hari-vickey/The-Eagle-Eye/ros_packages/swarmrobot/models/arena_s2/meshes/Stage2/texture.png

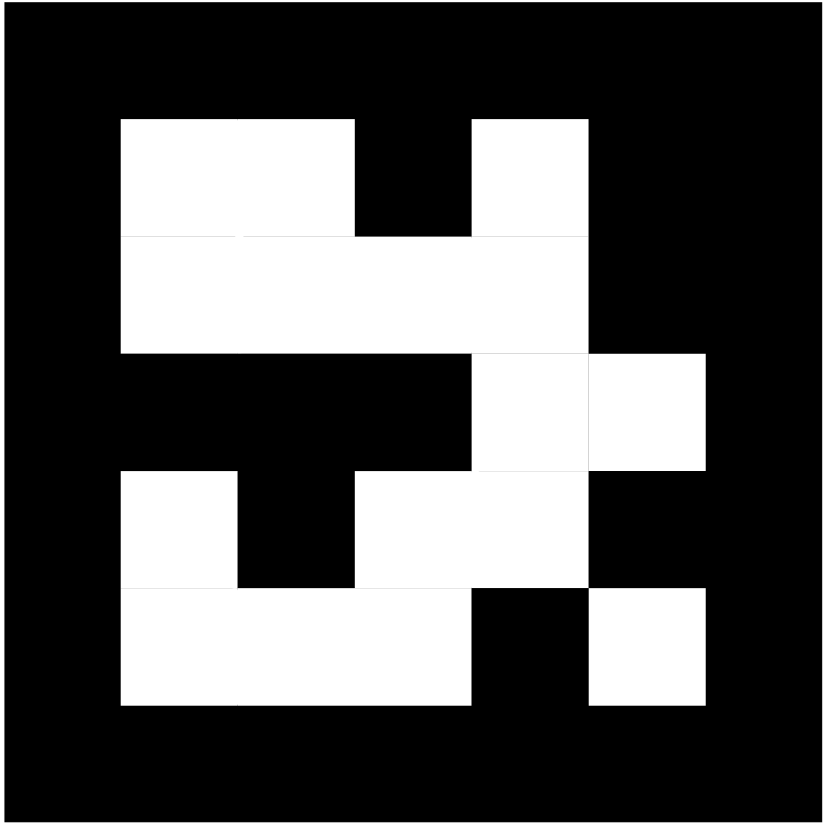
ros_packages/swarmrobot/models/arena_s2/meshes/Stage2/texture.png
