hari-vickey/The-Eagle-Eye/ros_packages/swarmrobot/models/arena_s2/meshes/Stage2/texture_6.png

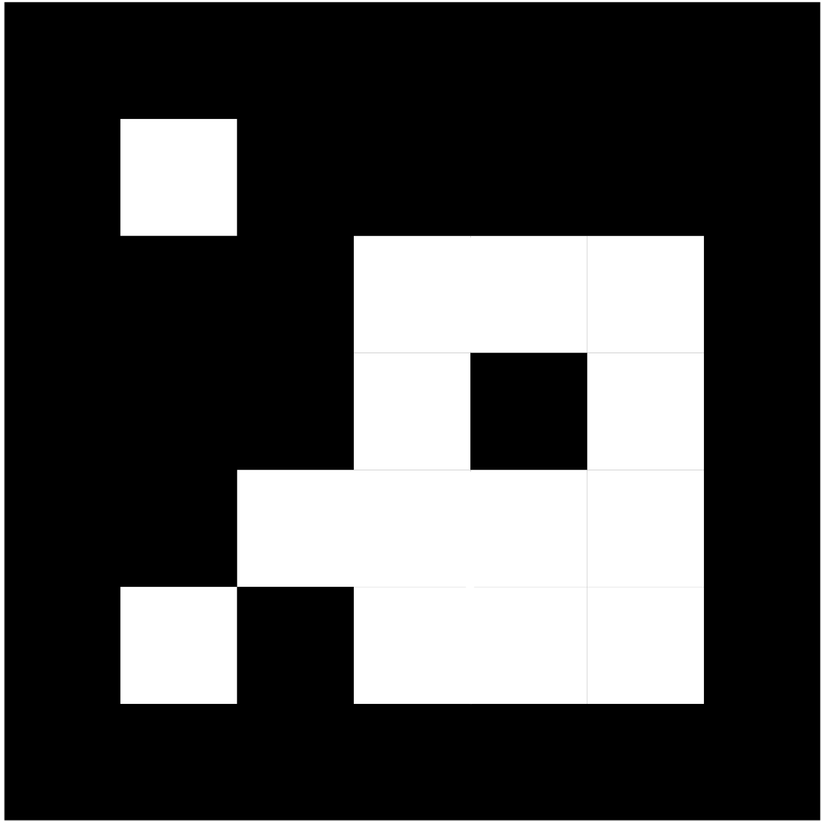
ros_packages/swarmrobot/models/arena_s2/meshes/Stage2/texture_6.png
