hari-vickey/The-Eagle-Eye/ros_packages/grid_bot_description/meshes/identifier_1.stl

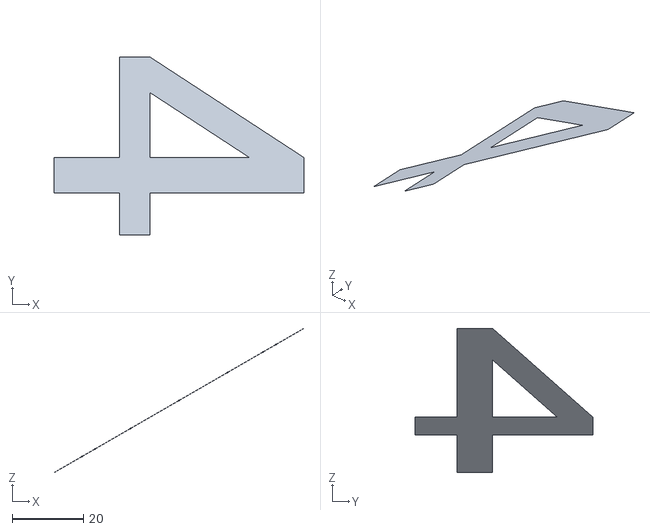
[picture p28: CAD file, 2021-12-07]
ros_packages/grid_bot_description/meshes/identifier_1.stl
70.4 x 50.0 x 40.7
