hari-vickey/The-Eagle-Eye/ros_packages/bot_description/grid_bot_3_description/meshes/identifier_1.stl

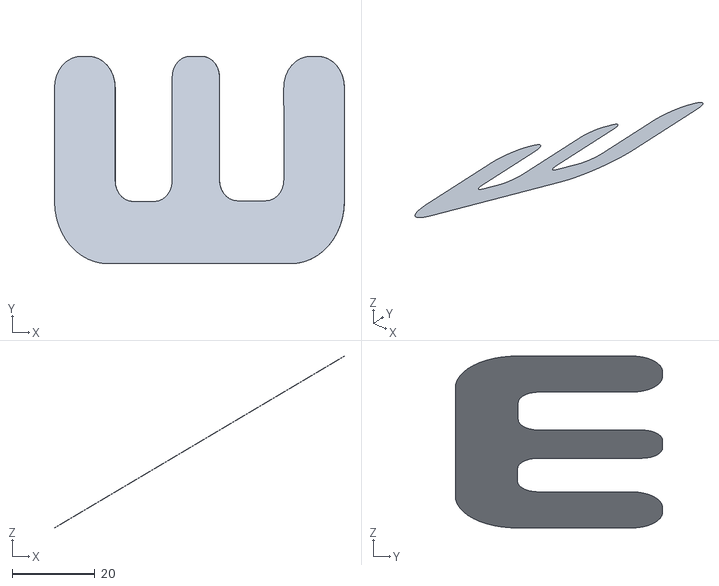
[picture p29: CAD file, 2021-12-07]
ros_packages/bot_description/grid_bot_3_description/meshes/identifier_1.stl
69.9 x 50.0 x 41.5
