hari-vickey/The-Eagle-Eye/ros_packages/bot_description/grid_bot_4_description/meshes/connector_rod_1.stl

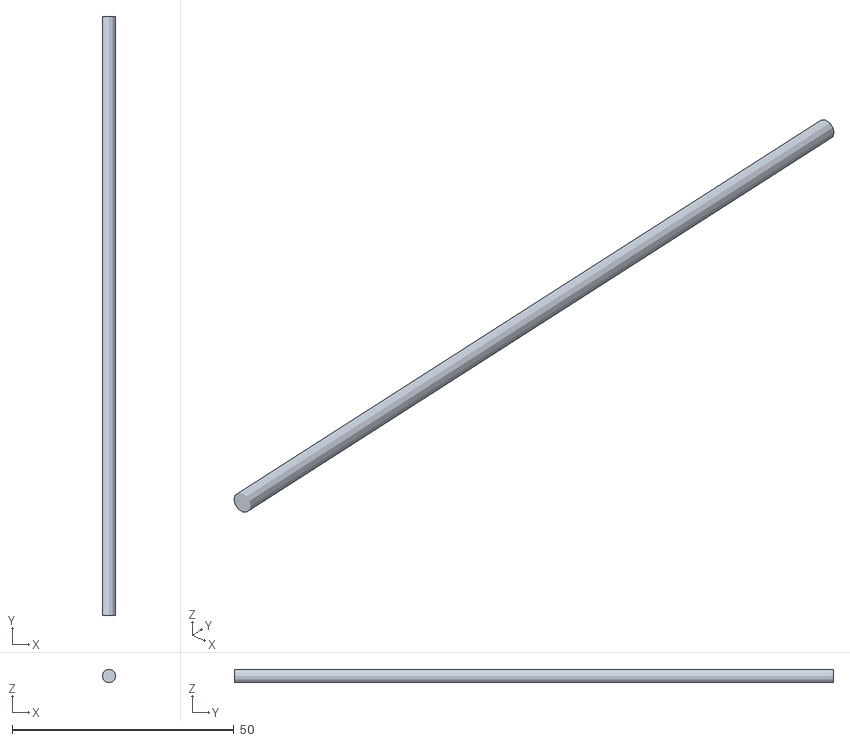
[picture p30: CAD file, 2021-12-07]
ros_packages/bot_description/grid_bot_4_description/meshes/connector_rod_1.stl
3.00 x 135.0 x 3.00
