hari-vickey/The-Eagle-Eye/ros_packages/grid_bot_description/meshes/side_pane_2.stl

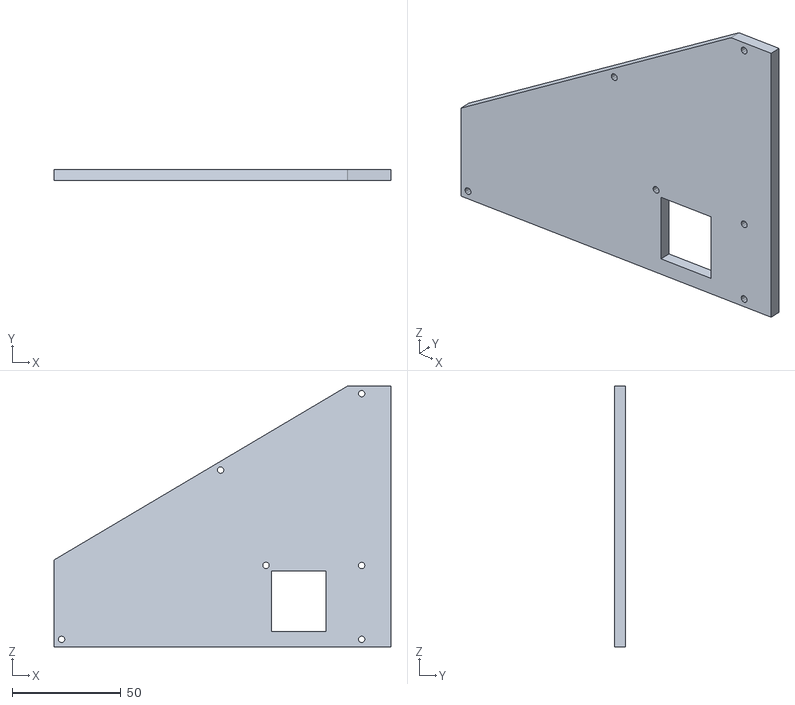
[picture p31: CAD file, 2021-12-07]
ros_packages/grid_bot_description/meshes/side_pane_2.stl
155.0 x 5.00 x 120.0
