hari-vickey/The-Eagle-Eye/ros_packages/bot_description/grid_bot_3_description/meshes/servo_actuator_1.stl

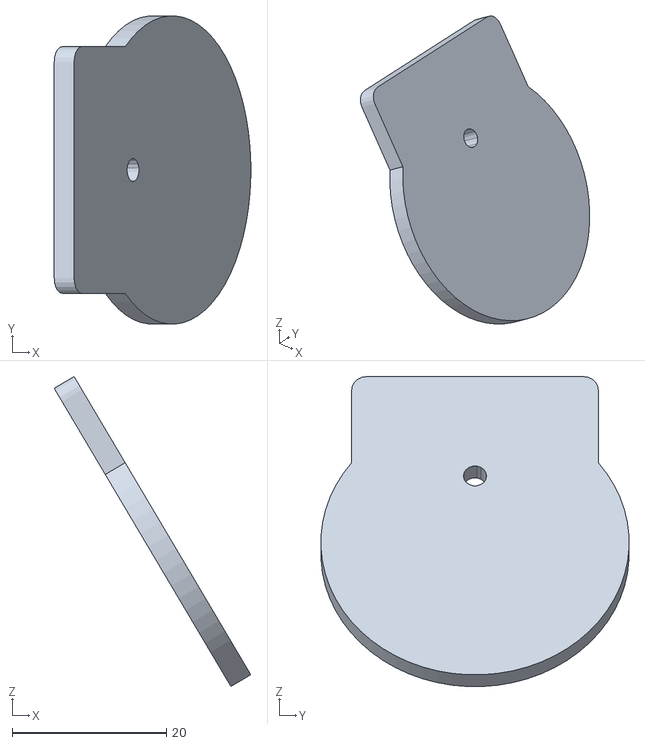
[picture p32: CAD file, 2021-12-07]
ros_packages/bot_description/grid_bot_3_description/meshes/servo_actuator_1.stl
25.5 x 40.0 x 40.2
