hari-vickey/The-Eagle-Eye/ros_packages/bot_description/grid_bot_4_description/meshes/identifier_1.stl

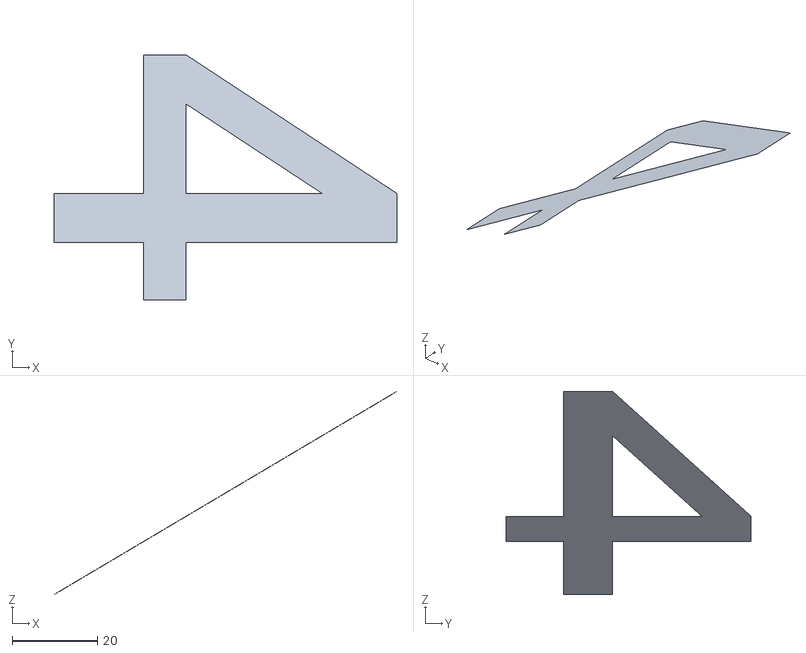
[picture p33: CAD file, 2021-12-07]
ros_packages/bot_description/grid_bot_4_description/meshes/identifier_1.stl
80.4 x 57.5 x 47.7
