hari-vickey/The-Eagle-Eye/ros_packages/grid_bot_description/meshes/base_link.stl

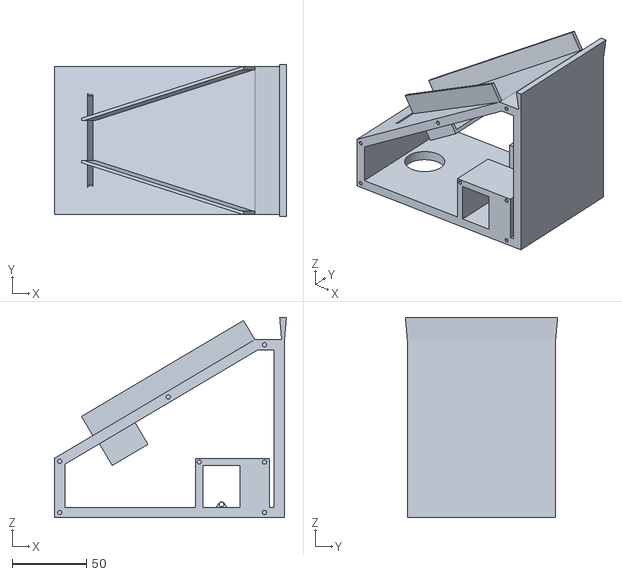
[picture p34: CAD file, 2021-12-07]
ros_packages/grid_bot_description/meshes/base_link.stl
156.3 x 102.6 x 135.0
