hari-vickey/The-Eagle-Eye/test_programs/images/check.png

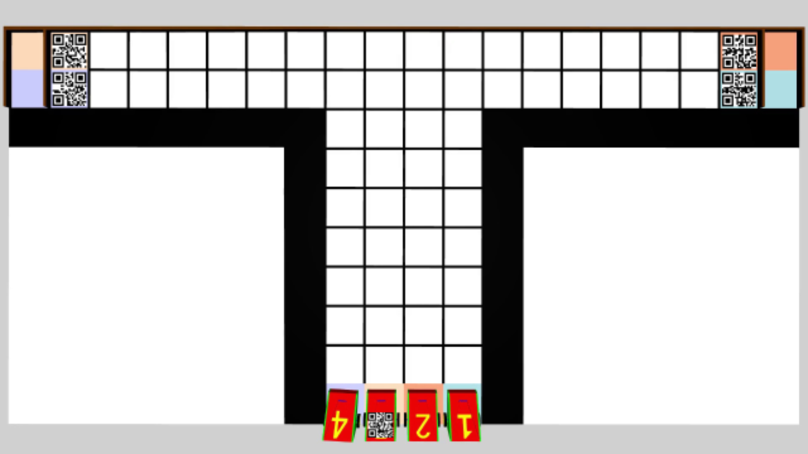
test_programs/images/check.png
