hari-vickey/The-Eagle-Eye/test_programs/images/img.png

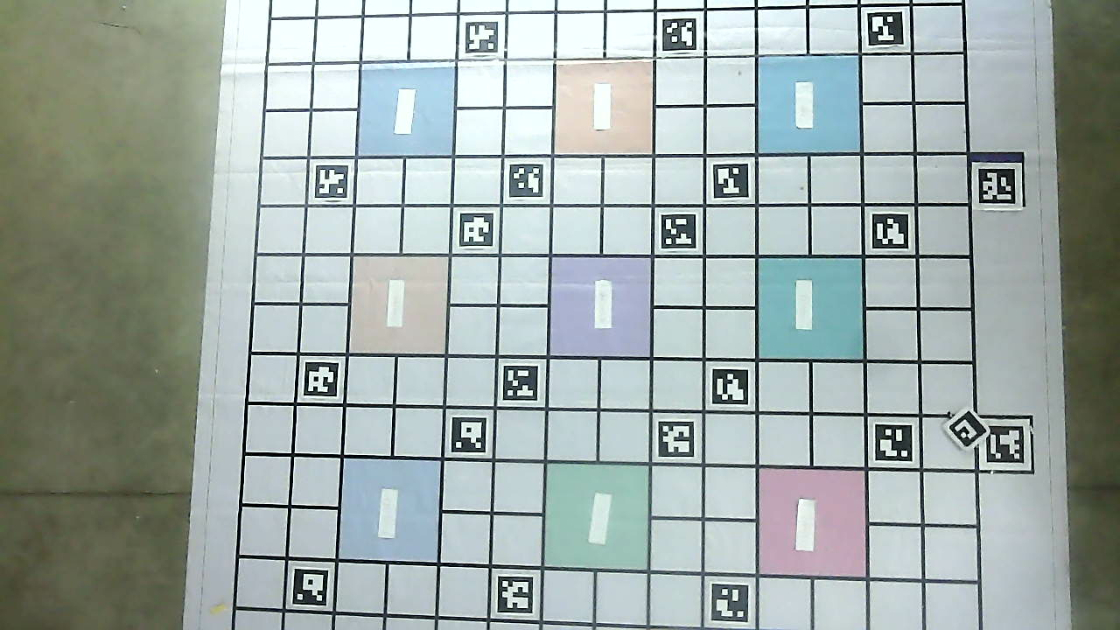
test_programs/images/img.png
